pu2clr/VFO_BFO_OLED_ARDUINO/images/20190330_130632.jpg

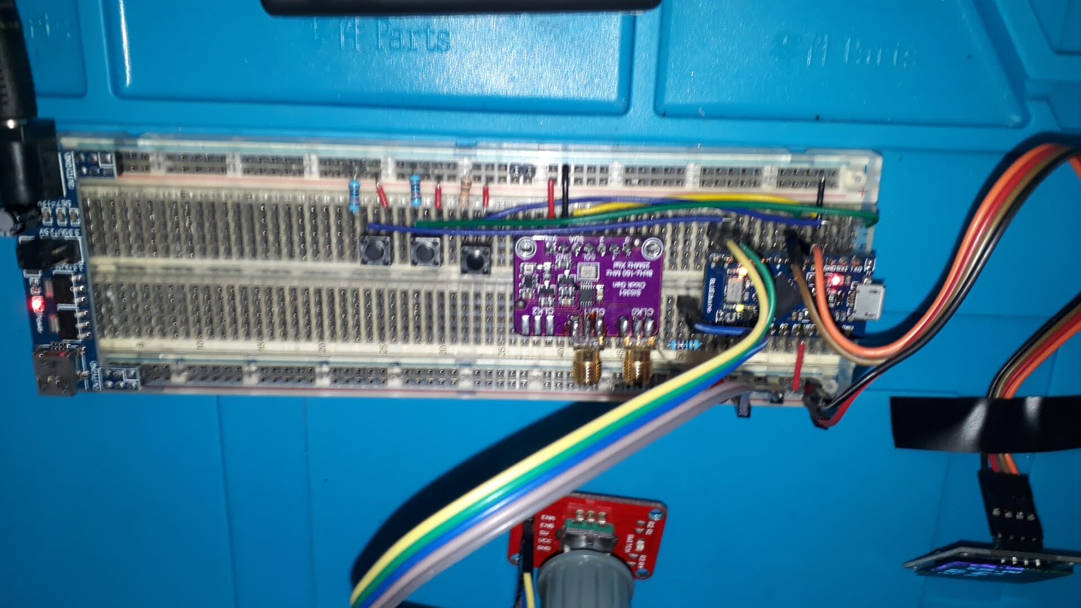
images/20190330_130632.jpg
