pu2clr/VFO_BFO_OLED_ARDUINO/images/20190330_130825.jpg

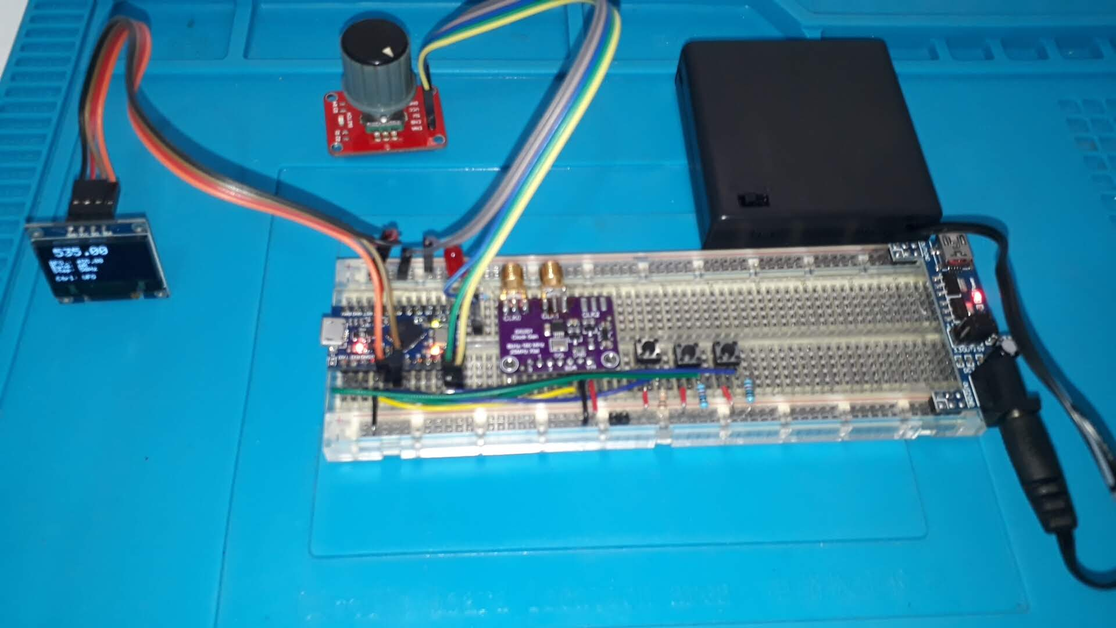
images/20190330_130825.jpg
