pu2clr/VFO_BFO_OLED_ARDUINO/images/20190330_131004.jpg

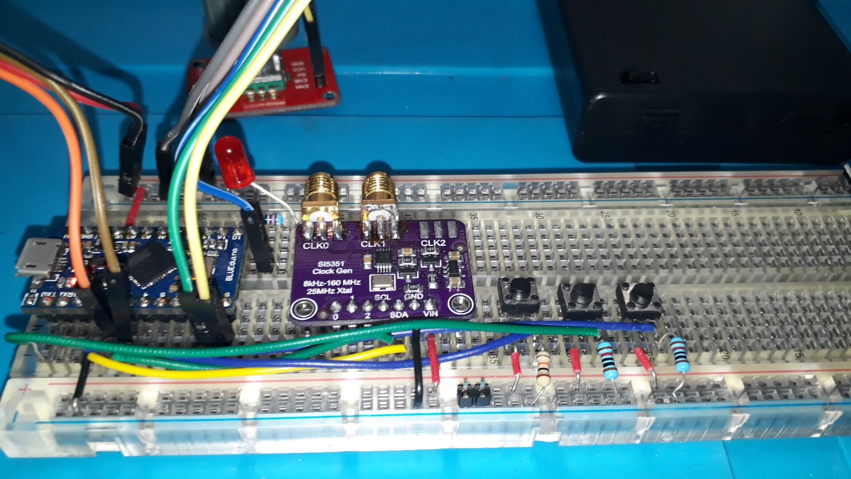
images/20190330_131004.jpg
