pu2clr/VFO_BFO_OLED_ARDUINO/images/dial_04.png

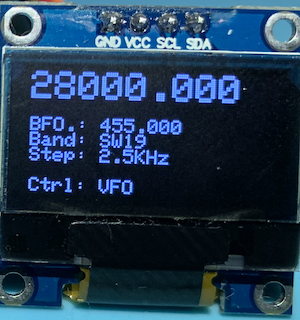
images/dial_04.png
