pu2clr/VFO_BFO_OLED_ARDUINO/images/dial_06.png

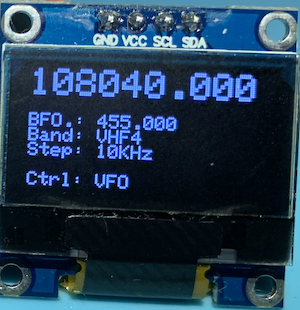
images/dial_06.png
