pu2clr/VFO_BFO_OLED_ARDUINO/Experiments/IRController/CheckYourRemoteControl/CheckYourRemoteControl.ino

#include <IRremote.h>

int RECV_PIN = 9;

// 
IRrecv irrecv(RECV_PIN);
decode_results results;

void setup()
{
  Serial.begin(9600);
  irrecv.enableIRIn(); // Initiate the IR Receiver

  Serial.println("Ready to receive...");
  Serial.println(".");
  
}

void loop()
{
  // Check the IR. Does it have something?  
  if (irrecv.decode(&results))
    { // If so.. 
     Serial.print("Take note. It is the code for this action: ");
     Serial.println(results.value);
     irrecv.resume(); // Ready to receive the next value
    }
}
